Nielsenfam/NightSky/case/one.dxf

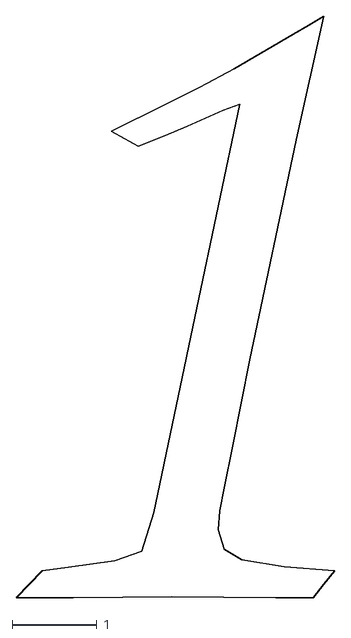
[picture p15: CAD file, 2013-06-14]
case/one.dxf
3.76 x 6.86
